kloper/st12/firmware/st12_term.h

/* -*- C -*-
 *
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
 * Copyright (c) 2021 Dimitry Kloper <kloper@users.sf.net>
 *
 * st12_term.h -- Minimal terminal graphics framework
 *
 */

#pragma once

#define TERM_FRAME_MAX_CHILDREN 16
#define TERM_COUNTER_MAX_WIDTH 8
#define TERM_LABEL_MAX_WIDTH 5

typedef enum _term_event { PRESS, FORWARD, BACKWARD, FOCUS, TICK } term_event_t;

struct _term_widget;
typedef uint32_t (*term_event_manager_t)(struct _term_widget *widget,
                                         term_event_t event,
                                         uint32_t event_data);

typedef uint32_t (*term_event_callback_t)(struct _term_widget *widget,
                                          uint32_t event_data);

typedef const char *(*term_render_callback_t)(struct _term_widget *widget);

typedef void (*term_action_callback_t)(uint8_t *data);

typedef struct _term_widget {
  term_event_manager_t on_event;
  term_event_callback_t on_press;
  term_event_callback_t on_forward;
  term_event_callback_t on_backward;
  term_event_callback_t on_focus;
  term_event_callback_t on_tick;
  term_render_callback_t render;
} term_widget_t;

typedef struct _term_label {
  term_widget_t base;
  const char *text;
} term_label_t;

typedef struct _term_int_label {
  term_label_t base;
  int value;
  char text[TERM_LABEL_MAX_WIDTH];
} term_int_label_t;

typedef struct _term_float_label {
  term_label_t base;
  int value;
  int divider;
  char text[TERM_LABEL_MAX_WIDTH];
} term_float_label_t;

typedef struct _term_st12_temp_label {
  term_widget_t base;
  int is_idle;
  const st12_config_t *config;
  int32_t temperature;
  uint32_t current;
  int overcurrent;
  char text[TERM_LABEL_MAX_WIDTH * 6];
} term_st12_temp_label_t;

typedef struct _term_button {
  term_widget_t base;
  const char *text;
  term_action_callback_t press_action;
  uint8_t *user_data;
  uint8_t inverse_text;
  uint8_t inverse_char;
} term_button_t;

typedef term_button_t term_grabber_t;

typedef struct _term_counter {
  term_button_t base;
  term_action_callback_t assign_action;
  uint8_t active;
  uint32_t min_value;
  uint32_t max_value;
  uint32_t value;
  uint8_t disp_width;
  char text[TERM_COUNTER_MAX_WIDTH + 1];
  uint8_t *user_data;
} term_counter_t;

typedef struct _term_frame {
  term_widget_t *children[TERM_FRAME_MAX_CHILDREN];
  uint8_t nchildren;
  uint8_t focus;
} term_frame_t;

void term_widget_init(term_widget_t *widget);
void term_label_init(term_label_t *widget, const char *text);
void term_frame_init(term_frame_t *frame);
void term_button_init(term_button_t *button, const char *text,
                      term_action_callback_t press_callback,
                      uint8_t *user_data);
int term_frame_add_child(term_frame_t *frame, term_widget_t *widget,
                         uint8_t focus);
uint32_t term_frame_dispatch(term_frame_t *frame, term_event_t event,
                             uint32_t event_data);
void term_frame_render(term_frame_t *frame);
void term_frame_reset(term_frame_t *frame);
void term_counter_init(term_counter_t *counter,
                       term_action_callback_t assign_action, uint32_t min_value,
                       uint32_t max_value, uint8_t disp_width,
                       uint8_t *user_data);
void term_grabber_init(term_grabber_t *grabber, const char *text,
                       term_action_callback_t press_callback,
                       uint8_t *user_data);
void term_int_label_init(term_int_label_t *widget, const char *format,
                         int value);
void term_float_label_init(term_float_label_t *widget, const char *format,
                           int value, int divider);
void term_st12_temp_label_init(term_st12_temp_label_t *widget,
                               const st12_config_t *config);
