kloper/st12/firmware/st12_linapprox.h

/** -*- C -*-
 * @file
 *
 * @brief Evaluate value of function based on its linear approximation
 *
 * This file is from https://github.com/kloper/thermo
 *
 * @page License
 *
 * Copyright (c) 2016, Dimitry Kloper.
 * All rights reserved.
 *
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
 * * Redistributions of source code must retain the above copyright
 * notice, this list of conditions and the following disclaimer.
 *
 * * Redistributions in binary form must reproduce the above copyright
 * notice, this list of conditions and the following disclaimer in the
 * documentation and/or other materials provided with the
 * distribution.
 *
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
 */

#pragma once

typedef struct _point {
  int32_t x;
  int32_t y;
} point_t;

int32_t linapprox(const point_t *const values, const int size, int32_t x);

/*
 * end of file
 */
